balassy/laser-temp-gun/case/Button/img.jpg

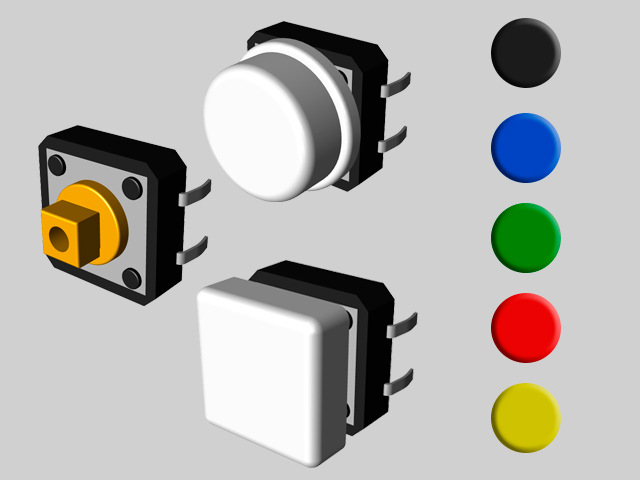
case/Button/img.jpg
