balassy/laser-temp-gun/case/Laser Diode/Photo1.jpg

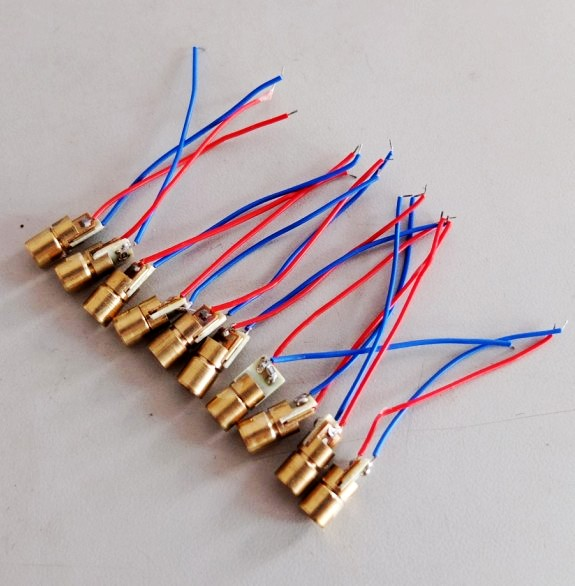
case/Laser Diode/Photo1.jpg
