balassy/laser-temp-gun/case/Laser Diode/Photo2.jpg

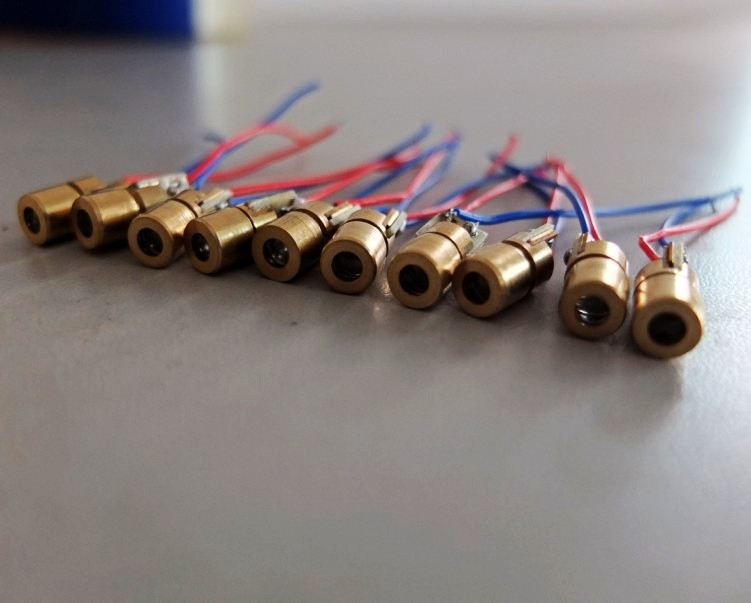
case/Laser Diode/Photo2.jpg
