balassy/laser-temp-gun/case/Pin header male/pin 8-2.54.jpg

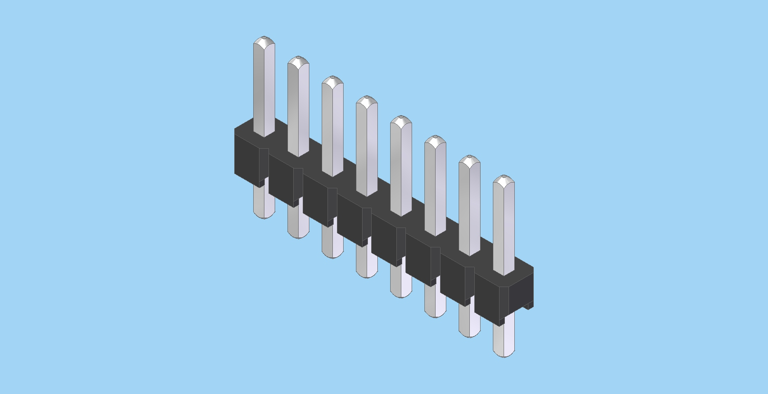
case/Pin header male/pin 8-2.54.jpg
