balassy/laser-temp-gun/case/Switch/10x15mm SPST 2pin on_off G130 Boat Rocker Switch 3A-250V.jpg

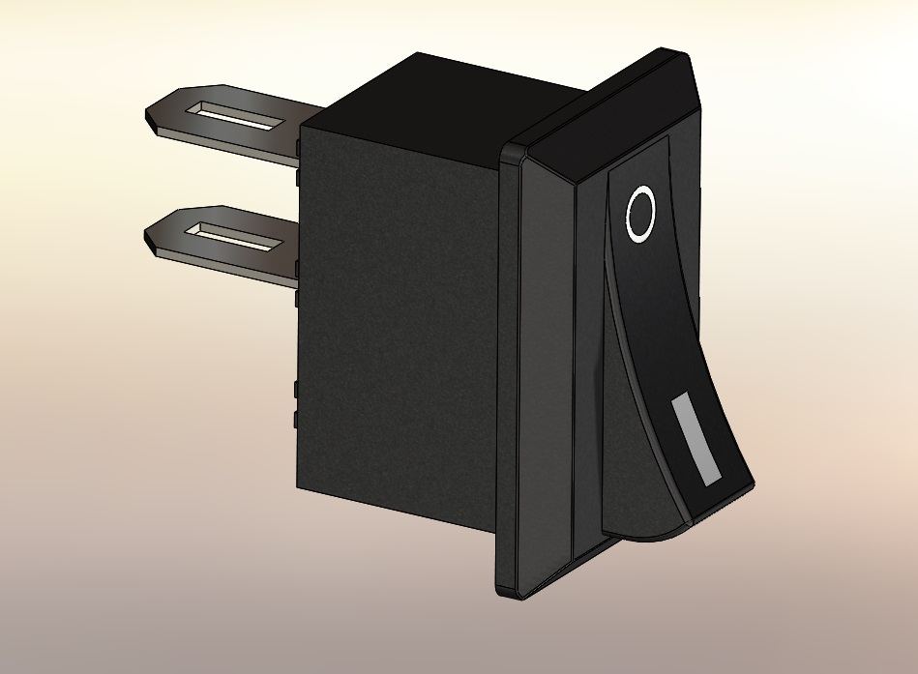
case/Switch/10x15mm SPST 2pin on_off G130 Boat Rocker Switch 3A-250V.jpg
