balassy/laser-temp-gun/case/Wemos OLED Shield 64x48/Wemos OLED Shield.jpg

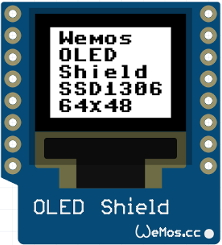
case/Wemos OLED Shield 64x48/Wemos OLED Shield.jpg
