balassy/laser-temp-gun/case/Button/12mmx12mm Without cap.stp

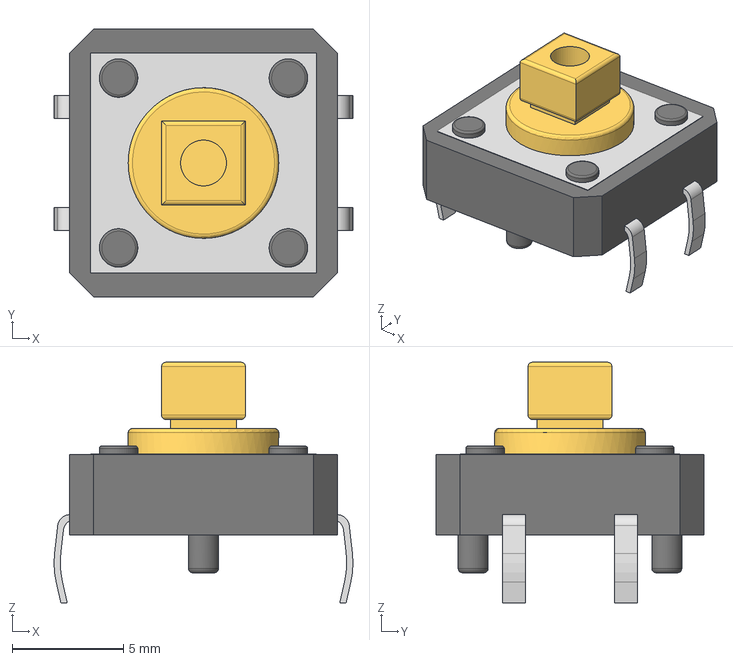
[picture p29: CAD file, 2020-03-14]
case/Button/12mmx12mm Without cap.stp
13.4 x 12.0 x 10.8 mm
